ZoharGalili/Sigma-HHKB/HHKB_PCB_V3/Matrix.kicad_sch

## KiCad design HHKB_PCB_V3/Matrix.kicad_sch (2024-08-05)

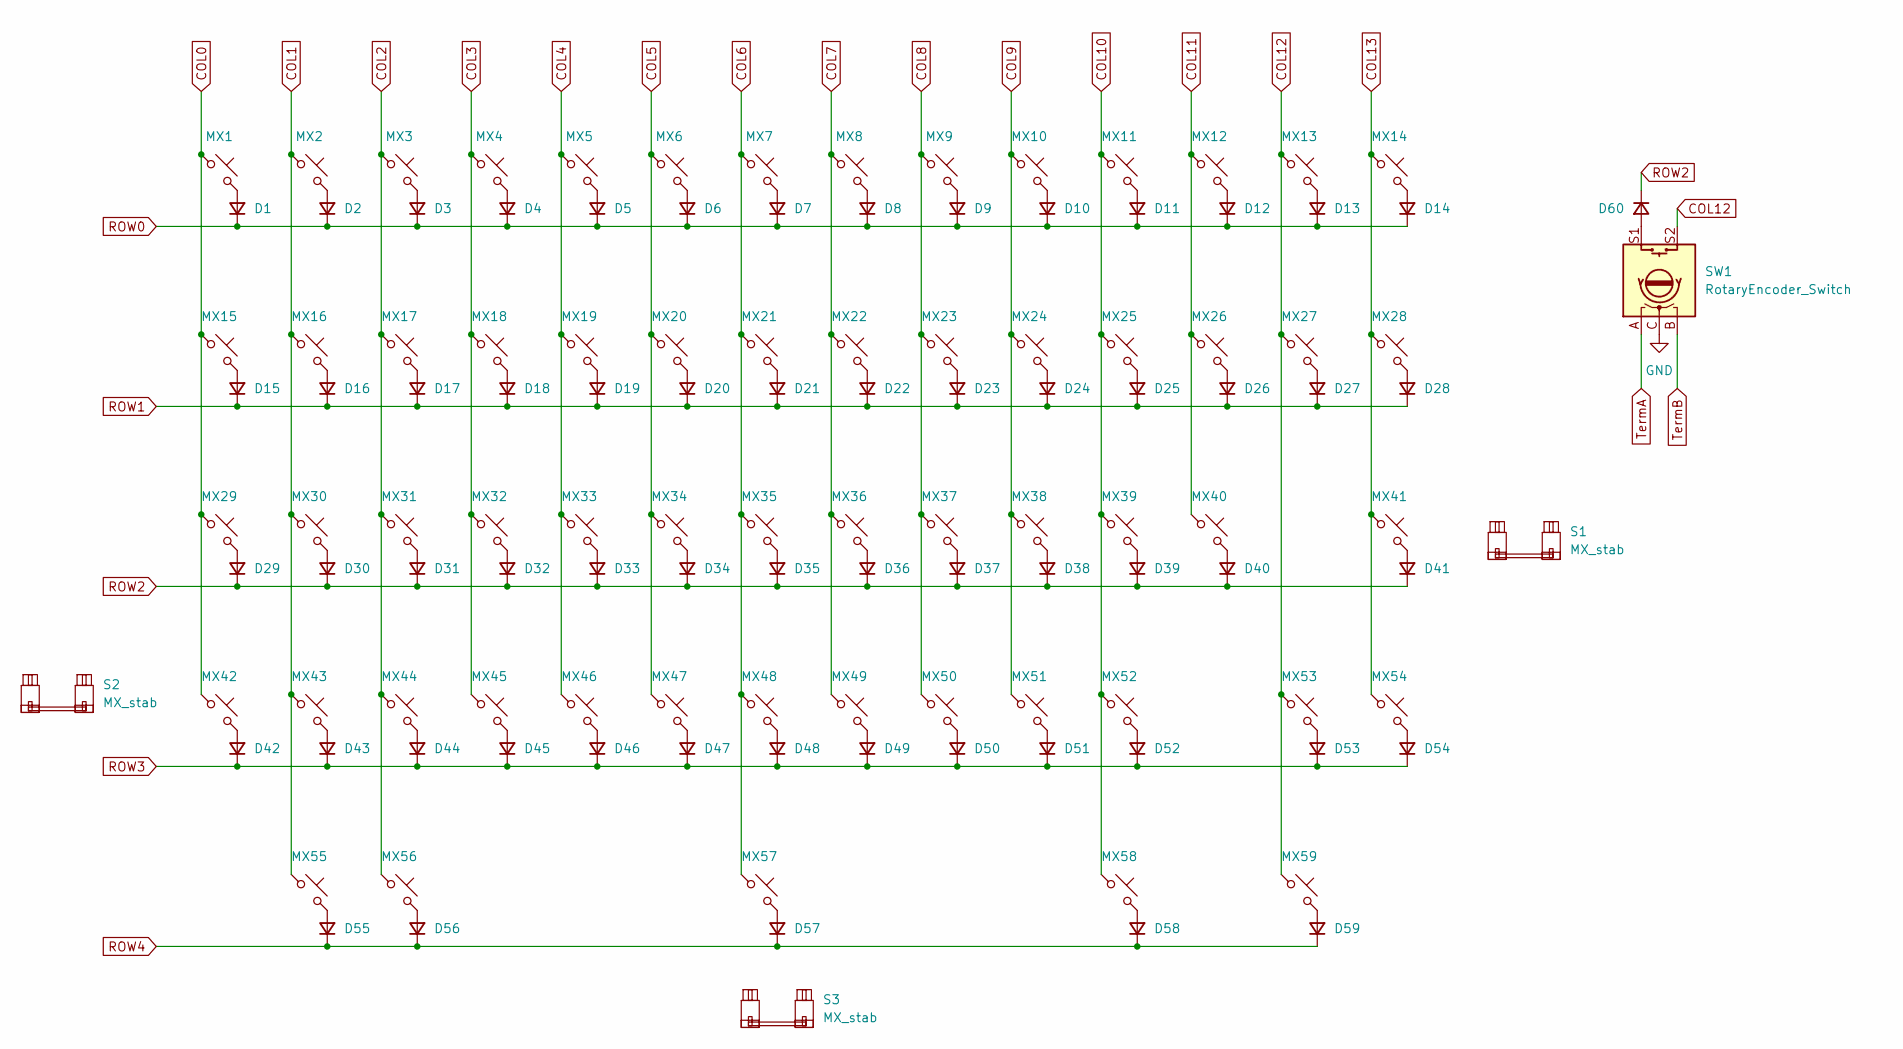
[picture p9: schematic Matrix.kicad_sch]

Parts:
D1, D2, D3, D4, D5, D6, D7, D8, D9, D10, D11, D12, D13, D14, D15, D16, D17, D18, D19, D20, D21, D22, D23, D24, D25, D26, D27, D28, D29, D30, D31, D32, D33, D34, D35, D36, D37, D38, D39, D40, D41, D42, D43, D44, D45, D46, D47, D48, D49, D50, D51, D52, D53, D54, D55, D56, D57, D58, D59, D60: D_Small; D_SOD-123
MX1, MX2, MX3, MX4, MX5, MX6, MX7, MX8, MX9, MX10, MX11, MX12, MX13, MX14, MX15, MX16, MX17, MX18, MX19, MX20, MX21, MX22, MX23, MX24, MX25, MX26, MX27, MX28, MX29, MX30, MX31, MX32, MX33, MX34, MX35, MX36, MX37, MX38, MX39, MX40, MX41, MX42, MX43, MX44, MX45, MX46, MX47, MX48, MX49, MX50, MX51, MX52, MX53, MX54, MX55, MX56, MX57, MX58, MX59: MX_SW_solder; SW_MX_HS_CPG151101S11_1u
S1, S2: MX_stab; STAB_MX_2.25u
S3: MX_stab; STAB_MX_7u
SW1: RotaryEncoder_Switch; ROT_Alps_EC11E-Switch

Connections:
COL0: MX1.1, MX15.1, MX29.1, MX42.1
COL1: MX2.1, MX16.1, MX30.1, MX43.1, MX55.1
COL2: MX3.1, MX17.1, MX31.1, MX44.1, MX56.1
COL3: MX4.1, MX18.1, MX32.1, MX45.1
COL4: MX5.1, MX19.1, MX33.1, MX46.1
COL5: MX6.1, MX20.1, MX34.1, MX47.1
COL6: MX7.1, MX21.1, MX35.1, MX48.1, MX57.1
COL7: MX8.1, MX22.1, MX36.1, MX49.1
COL8: MX9.1, MX23.1, MX37.1, MX50.1
COL9: MX10.1, MX24.1, MX38.1, MX51.1
COL10: MX11.1, MX25.1, MX39.1, MX52.1, MX58.1
COL11: MX12.1, MX26.1, MX40.1
COL12: MX13.1, MX27.1, MX53.1, MX59.1, SW1.S2
COL13: MX14.1, MX28.1, MX41.1, MX54.1
GND: SW1.C
unnamed: D1.2 (A), MX1.2
unnamed: D2.2 (A), MX2.2
unnamed: D3.2 (A), MX3.2
unnamed: D4.2 (A), MX4.2
unnamed: D5.2 (A), MX5.2
unnamed: D6.2 (A), MX6.2
unnamed: D7.2 (A), MX7.2
unnamed: D8.2 (A), MX8.2
unnamed: D9.2 (A), MX9.2
unnamed: D10.2 (A), MX10.2
unnamed: D11.2 (A), MX11.2
unnamed: D12.2 (A), MX12.2
unnamed: D13.2 (A), MX13.2
unnamed: D14.2 (A), MX14.2
unnamed: D15.2 (A), MX15.2
unnamed: D16.2 (A), MX16.2
unnamed: D17.2 (A), MX17.2
unnamed: D18.2 (A), MX18.2
unnamed: D19.2 (A), MX19.2
unnamed: D20.2 (A), MX20.2
unnamed: D21.2 (A), MX21.2
unnamed: D22.2 (A), MX22.2
unnamed: D23.2 (A), MX23.2
unnamed: D24.2 (A), MX24.2
unnamed: D25.2 (A), MX25.2
unnamed: D26.2 (A), MX26.2
unnamed: D27.2 (A), MX27.2
unnamed: D28.2 (A), MX28.2
unnamed: D29.2 (A), MX29.2
unnamed: D30.2 (A), MX30.2
unnamed: D31.2 (A), MX31.2
unnamed: D32.2 (A), MX32.2
unnamed: D33.2 (A), MX33.2
unnamed: D34.2 (A), MX34.2
unnamed: D35.2 (A), MX35.2
unnamed: D36.2 (A), MX36.2
unnamed: D37.2 (A), MX37.2
unnamed: D38.2 (A), MX38.2
unnamed: D39.2 (A), MX39.2
unnamed: D40.2 (A), MX40.2
unnamed: D41.2 (A), MX41.2
unnamed: D42.2 (A), MX42.2
unnamed: D43.2 (A), MX43.2
unnamed: D44.2 (A), MX44.2
unnamed: D45.2 (A), MX45.2
unnamed: D46.2 (A), MX46.2
unnamed: D47.2 (A), MX47.2
unnamed: D48.2 (A), MX48.2
unnamed: D49.2 (A), MX49.2
unnamed: D50.2 (A), MX50.2
unnamed: D51.2 (A), MX51.2
unnamed: D52.2 (A), MX52.2
unnamed: D53.2 (A), MX53.2
unnamed: D54.2 (A), MX54.2
unnamed: D55.2 (A), MX55.2
unnamed: D56.2 (A), MX56.2
unnamed: D57.2 (A), MX57.2
unnamed: D58.2 (A), MX58.2
unnamed: D59.2 (A), MX59.2
unnamed: D60.2 (A), SW1.S1
ROW0: D1.1 (K), D2.1 (K), D3.1 (K), D4.1 (K), D5.1 (K), D6.1 (K), D7.1 (K), D8.1 (K), D9.1 (K), D10.1 (K), D11.1 (K), D12.1 (K), D13.1 (K), D14.1 (K)
ROW1: D15.1 (K), D16.1 (K), D17.1 (K), D18.1 (K), D19.1 (K), D20.1 (K), D21.1 (K), D22.1 (K), D23.1 (K), D24.1 (K), D25.1 (K), D26.1 (K), D27.1 (K), D28.1 (K)
ROW2: D29.1 (K), D30.1 (K), D31.1 (K), D32.1 (K), D33.1 (K), D34.1 (K), D35.1 (K), D36.1 (K), D37.1 (K), D38.1 (K), D39.1 (K), D40.1 (K), D41.1 (K), D60.1 (K)
ROW3: D42.1 (K), D43.1 (K), D44.1 (K), D45.1 (K), D46.1 (K), D47.1 (K), D48.1 (K), D49.1 (K), D50.1 (K), D51.1 (K), D52.1 (K), D53.1 (K), D54.1 (K)
ROW4: D55.1 (K), D56.1 (K), D57.1 (K), D58.1 (K), D59.1 (K)
TermA: SW1.A
TermB: SW1.B
